nhchiu/3DPrinter-Designs/ProtoXtruder_2.0/Images/Render2.jpg

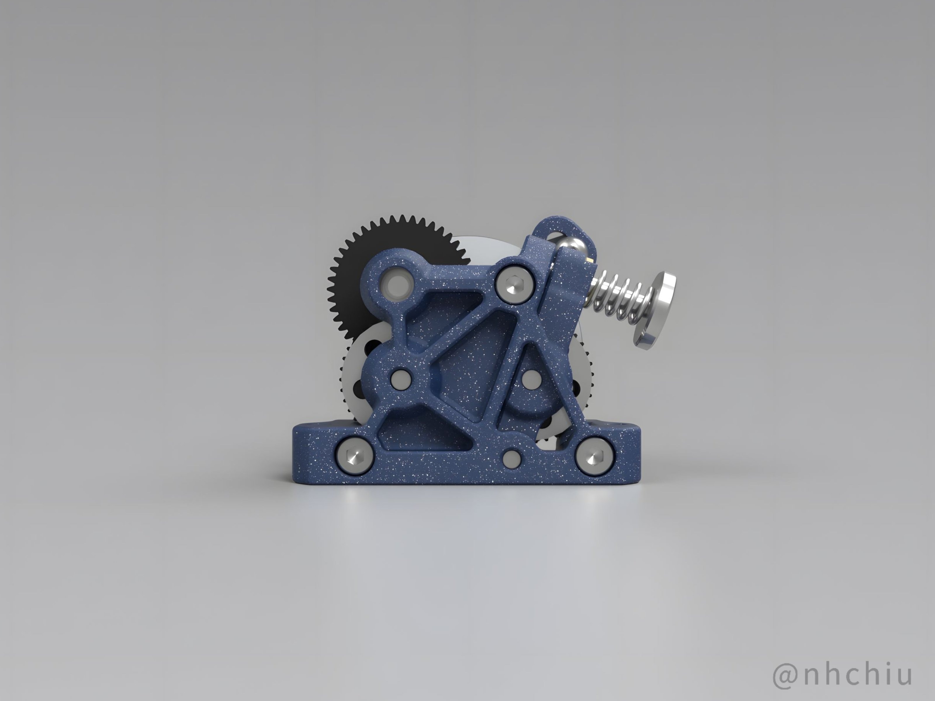
ProtoXtruder_2.0/Images/Render2.jpg
