nhchiu/3DPrinter-Designs/MiniSB_Draco/STLs/Hotend Mounts/Standard/Hotend Mount Dragon.stl

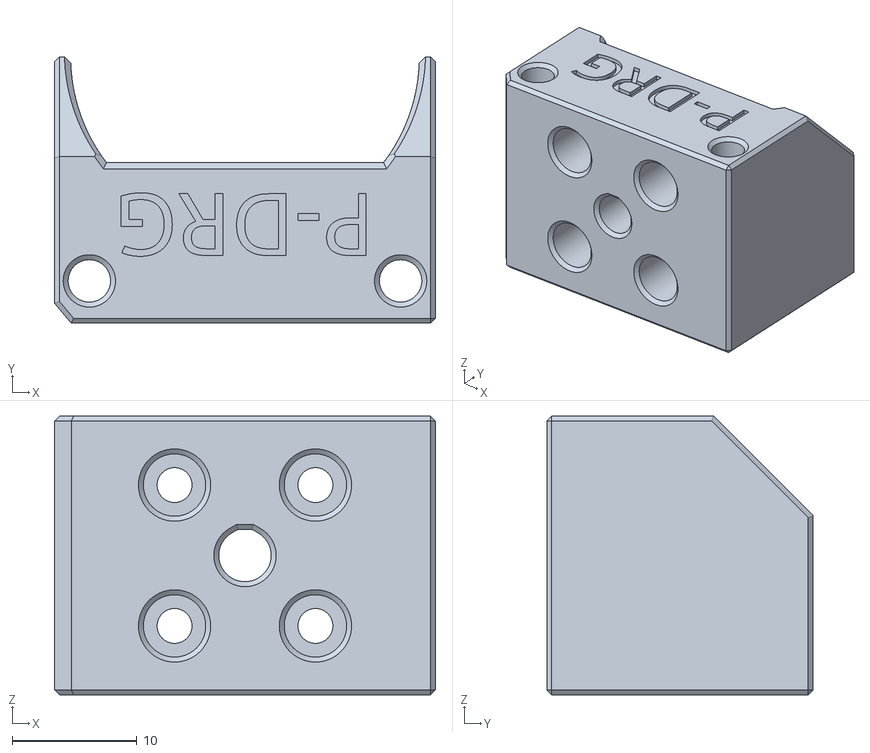
[picture p35: CAD file, 2026-01-24]
MiniSB_Draco/STLs/Hotend Mounts/Standard/Hotend Mount Dragon.stl
30.6 x 21.4 x 22.4
